WolfmannxD/Tee-Thermometer/Code/include/TeaTimer.h

#ifndef _TEATIMER_H_
#define _TEATIMER_H_
// #include <Arduino.h>
#include <iostream>
#include <queue>
// #include <stdlib.h>

class TeaTimer;          // main class
class Parameters;        // hold config parameters
class TemperatureSensor; // provides interface to sensor
class SerialTempInput;   // simulates sensor with received data
class SerialOutput;      // print output over serial
class SerialInterface;   // handles serial communication
class MQTTOutput;        // publish temperature and times via mqtt
class OledDisplay;       // show data on display
class WebServer;         // provide simple website with data and config

class DataInput;  // interface for input classes
class DataOutput; // interface for output classes

// Interfaces

/*
Data input is handled by a get-method that returns 
a temperature value. 
*/
class DataInput
{
public:
    virtual double getTemperature() = 0;
};

/*
The different data output channels use a single
method to update the displayed or transferred data.
*/
class DataOutput
{
public:
    virtual void updateDisplay(
        double &temperature,
        double &timeDrink,
        double &timeCold) = 0;
};

/*
Wrap the builtin Serial class and parse incoming
messages. Provide methods for input and output.
*/
class SerialInterface
{
public:
    bool initSuccessful{false}; // Was the initialization successful?
    std::queue<double> TInput{};
    /*
    Instantiate serial connection and maybe 
    check if something is connected.
    */
    SerialInterface()
    {
        Serial.begin(9600); // can not fail
        // ...               // <-- this can maybe fail?
        initSuccessful = true;
    }

    void write_str(String data)
    {
        Serial.println(data);
    }

    void write_double(double data)
    {
        Serial.println(data);
    }

    // can we use serialEvent ?
    void handleSerial()
    {
        String received;
        String prefix;
        String content;
        while (Serial.available() > 0)
        {
            received = Serial.readStringUntil(char('\n'));
            prefix = received.substring(0, 4);
            content = received.substring(4);
            if (prefix == "data")
            {
                // add temperature data
                TInput.push(std::stod(content.c_str())); // convert string to double
                Serial.println("Added " + content + " to the temperature queue.");
            }
            else if (prefix == "comm")
            {
                // execute command
            }
        };
    }
};

/*
Provide simulated temperature values via 
serial input.
*/
class SerialTempInput
{
private:
    SerialInterface *serial;

public:
    SerialTempInput(SerialInterface *SerialIF)
    {
        serial = SerialIF;
    }
    SerialTempInput()
    {
        SerialInterface serial = SerialInterface();
        serial.write_str("Falscher constructor");
    }

    double getTemperature()
    {
        double temp;
        if (serial->TInput.empty())
        {
            temp = 25.5;
        }
        else
        {
            temp = serial->TInput.front();
            serial->TInput.pop();
        }
        return temp;
    }
};
#endif
